epccs/RPUpi/Hardware/Design/MultiDrop.sch

## EAGLE design Hardware/Design/MultiDrop.sch (2018-09-16)

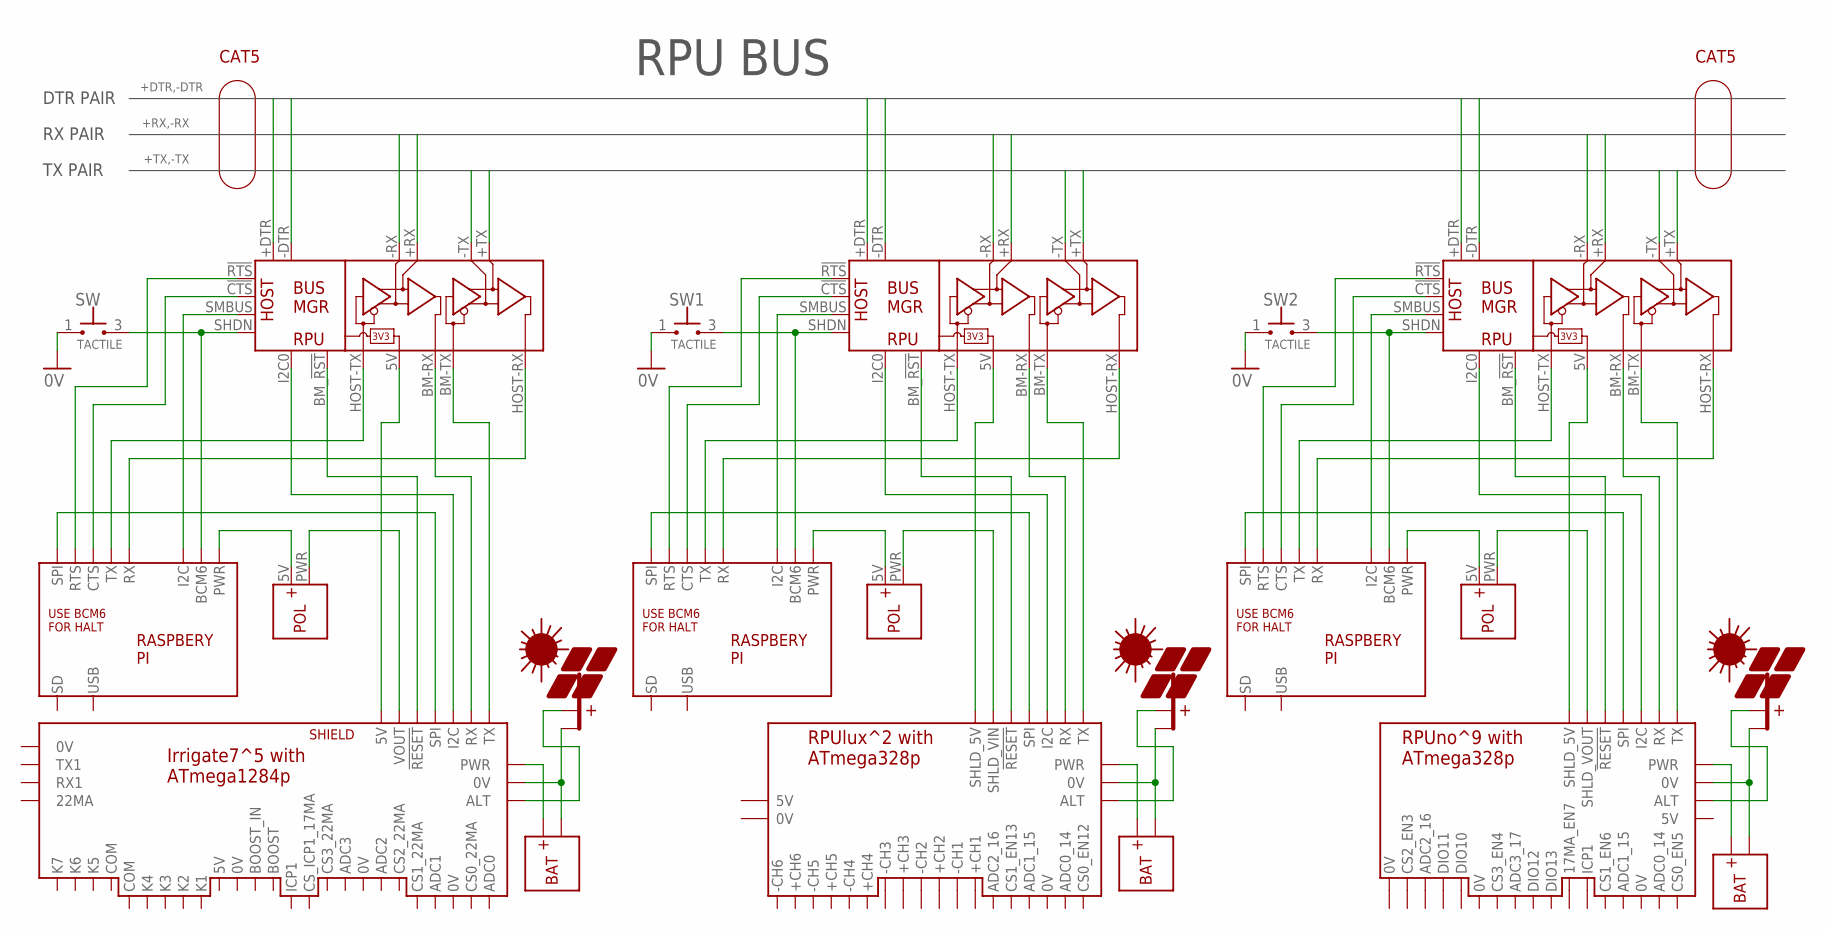
[picture p39: schematic MultiDrop.sch]

Parts:
BM1: RPUNO; NA-30
PV1, PV2, PV4: PV; NA-30
SW, SW1, SW2: TACTILE; KS11
U$1: IRRIGATE7; WITH_RPU_NAMES
U$2: RPULUX; WITH_RPU_NAMES
U$3, U$6, U$8: BUS_MGR; WITH_RPU_NAMES
U$4, U$7, U$9: BAT; NA-30
U$5, U$10, U$11: PI; NA-30
U$12, U$13, U$14: POL; WITH_RPU_NAMES

Connections:
0V: SW.1, SW1.1, SW2.1
+DTR: U$8.+DTR
+DTR1: U$3.+DTR
+DTR2: U$6.+DTR
+RX: U$8.+RX
+RX1: U$3.+RX
+RX2: U$6.+RX
+TX: U$8.+TX
+TX1: U$3.+TX
+TX2: U$6.+TX
-DTR: U$8.-DTR
-DTR1: U$3.-DTR
-DTR2: U$6.-DTR
-RX: U$8.-RX
-RX1: U$3.-RX
-RX2: U$6.-RX
-TX: U$8.-TX
-TX1: U$3.-TX
-TX2: U$6.-TX
unnamed: U$1.TX, U$8.BM-TX (BM_TX)
unnamed: U$1.RX, U$8.BM-RX (BM_RX)
unnamed: U$1.SHLD_VOUT (VOUT), U$12.PWR (VIN)
unnamed: U$8.SMBUS, U$11.8 (I2C)
unnamed: SW.3, U$8.SHDN, U$11.7 (BCM6)
unnamed: U$1.SPI, U$11.10 (SPI)
unnamed: PV1.2 (-PV), U$1.0V@PWR (0V), U$4.2 (-BAT)
unnamed: U$8.HOST-RX (HOST_RX), U$11.3 (RX)
unnamed: U$8.HOST-TX (HOST_TX), U$11.4 (TX)
unnamed: U$2.TX, U$3.BM-TX (BM_TX)
unnamed: U$2.RX, U$3.BM-RX (BM_RX)
unnamed: U$1.PWR, U$4.1 (+BAT)
unnamed: U$8.!CTS, U$11.1 (CTS)
unnamed: U$3.HOST-RX (HOST_RX), U$5.3 (RX)
unnamed: PV1.1 (+PV), U$1.AUX (ALT)
unnamed: U$8.!RTS, U$11.2 (RTS)
unnamed: U$3.HOST-TX (HOST_TX), U$5.4 (TX)
unnamed: U$2.SHLD_5V, U$3.5V (PWR)
unnamed: U$2.!RESET, U$3.BM_!RST! (BM-!RST!)
unnamed: U$2.I2C, U$3.I2C0
unnamed: U$2.SHLD_VOUT (SHLD_VIN), U$13.PWR (VIN)
unnamed: U$2.SPI, U$5.10 (SPI)
unnamed: U$3.SMBUS, U$5.8 (I2C)
unnamed: SW1.3, U$3.SHDN, U$5.7 (BCM6)
unnamed: U$3.!CTS, U$5.1 (CTS)
unnamed: U$3.!RTS, U$5.2 (RTS)
unnamed: BM1.1 (TX), U$6.BM-TX (BM_TX)
unnamed: BM1.2 (RX), U$6.BM-RX (BM_RX)
unnamed: U$1.SHLD_5V (5V), U$8.5V (PWR)
unnamed: U$1.!RESET, U$8.BM_!RST! (BM-!RST!)
unnamed: U$6.HOST-RX (HOST_RX), U$10.3 (RX)
unnamed: U$6.HOST-TX (HOST_TX), U$10.4 (TX)
unnamed: U$1.I2C, U$8.I2C0
unnamed: BM1.6 (SHLD_5V), U$6.5V (PWR)
unnamed: BM1.5 (!RESET), U$6.BM_!RST! (BM-!RST!)
unnamed: BM1.3 (I2C), U$6.I2C0
unnamed: BM1.7 (SHLD_VOUT), U$14.PWR (VIN)
unnamed: BM1.4 (SPI), U$10.10 (SPI)
unnamed: U$6.SMBUS, U$10.8 (I2C)
unnamed: SW2.3, U$6.SHDN, U$10.7 (BCM6)
unnamed: U$6.!CTS, U$10.1 (CTS)
unnamed: U$6.!RTS, U$10.2 (RTS)
unnamed: PV2.2 (-PV), U$2.0V@PWR (0V), U$9.2 (-BAT)
unnamed: U$2.PWR, U$9.1 (+BAT)
unnamed: PV2.1 (+PV), U$2.AUX (ALT)
unnamed: BM1.9 (0V), PV4.2 (-PV), U$7.2 (-BAT)
unnamed: BM1.8 (PWR), U$7.1 (+BAT)
unnamed: BM1.20 (ALT), PV4.1 (+PV)
unnamed: U$10.12 (PWR), U$14.5V
unnamed: U$5.12 (PWR), U$13.5V
unnamed: U$11.12 (PWR), U$12.5V

Notes on the sheet:
CAT5
DTR PAIR
RX PAIR
TX PAIR
RPU BUS
