epccs/RPUpi/Hardware/Design/Pi2AVR.sch

## EAGLE design Hardware/Design/Pi2AVR.sch (2018-09-16)

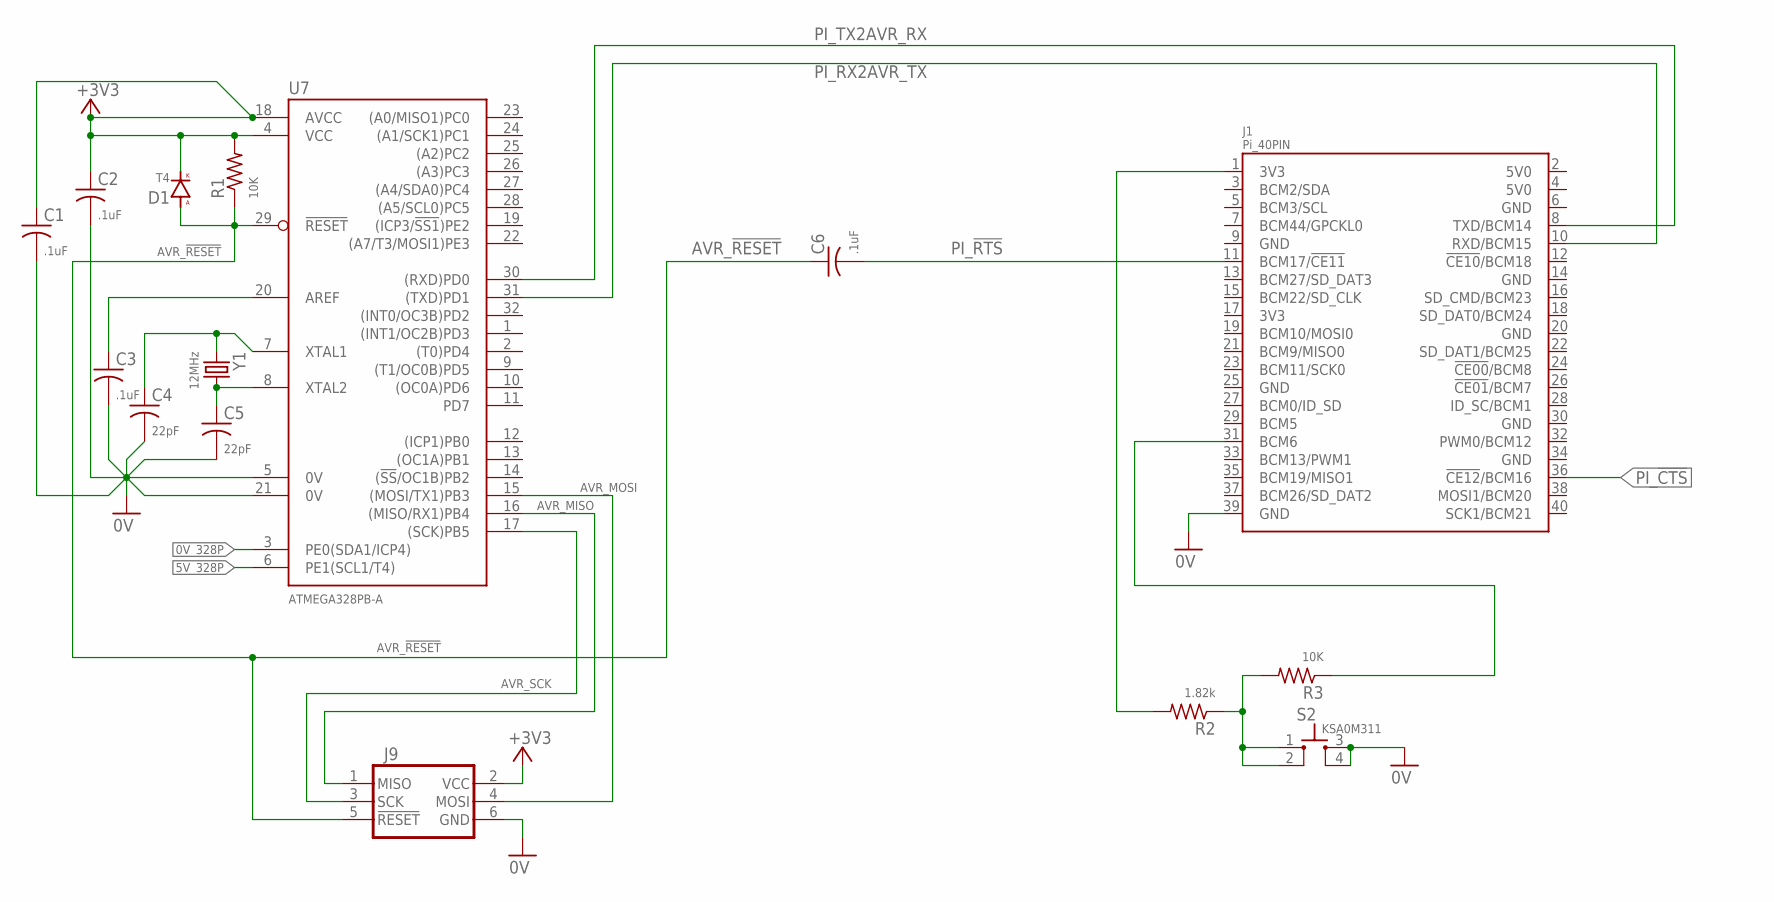
[picture p40: schematic Pi2AVR.sch]

Parts:
C1, C2, C3, C6: .1uF; C0603(1608)
C4, C5: 22pF; C0603(1608)
D1: T4; SOD123
J1: Pi_40PIN; RASPI_ZERO_V40PIN
J9: ISP-SPIPTH; ISP
R1, R3: 10K; C0805(2012)
R2: 1.82k; C0805(2012)
S2: KSA0M311; 0M311
U7: ATMEGA328PB-A; TQFP32-08
Y1: 12MHz; CSM-3X

Connections:
0V: C1.2, C2.2, C3.2, C4.2, C5.2, J1.39 (GND), J9.6 (GND), S2.3, S2.4, U7.5 (0V), U7.21 (0V)
0V_328P: U7.3 (PE0(SDA1/ICP4))
3V3@1: J1.1 (3V3), R2.2
5V_328P: U7.6 (PE1(SCL1/T4))
+3V3: C1.1, C2.1, D1.C (K), J9.2 (VCC), R1.2, U7.4 (VCC), U7.18 (AVCC)
AVR_!RESET: C6.1, D1.A, J9.5 (!RESET), R1.1, U7.29 (!RESET)
AVR_MISO: J9.1 (MISO), U7.16 ((MISO/RX1)PB4)
AVR_MOSI: J9.4 (MOSI), U7.15 ((MOSI/TX1)PB3)
AVR_SCK: J9.3 (SCK), U7.17 ((SCK)PB5)
MGR_AREF: C3.1, U7.20 (AREF)
unnamed: J1.31 (BCM6), R3.1
unnamed: R2.1, R3.2, S2.1, S2.2
PI_!CTS!: J1.36 (!CE12!/BCM16)
PI_!RTS!: C6.2, J1.11 (BCM17/!CE11!)
PI_RX2AVR_TX: J1.10 (RXD/BCM15), U7.31 ((TXD)PD1)
PI_TX2AVR_RX: J1.8 (TXD/BCM14), U7.30 ((RXD)PD0)
XTAL1: C4.1, U7.7 (XTAL1), Y1.1
XTAL2: C5.1, U7.8 (XTAL2), Y1.2
