epccs/RPUpi/Hardware/Design/Pi2AVR_wIOFF.sch

## EAGLE design Hardware/Design/Pi2AVR_wIOFF.sch (2018-09-16)

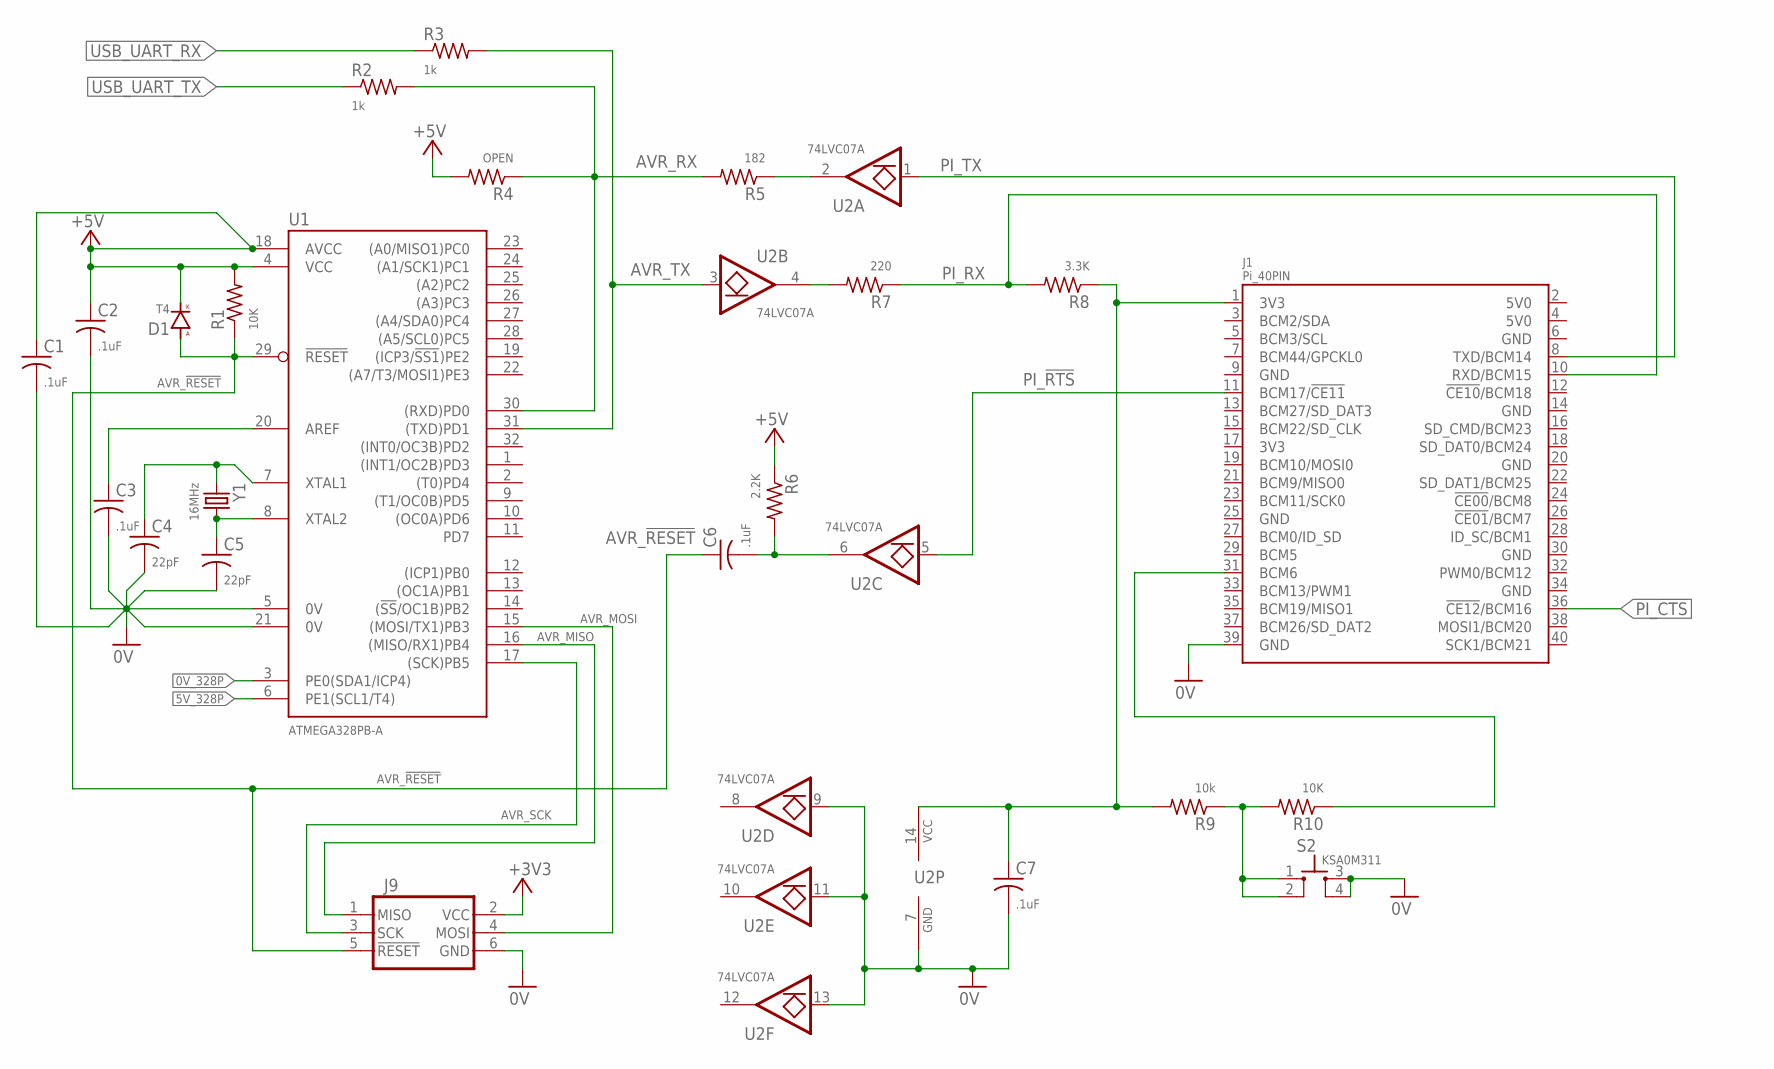
[picture p41: schematic Pi2AVR_wIOFF.sch]

Parts:
C1, C2, C3, C6, C7: .1uF; C0603(1608)
C4, C5: 22pF; C0603(1608)
D1: T4; SOD123
J1: Pi_40PIN; RASPI_ZERO_V40PIN
J9: ISP-SPIPTH; ISP
R1, R10: 10K; C0805(2012)
R2, R3: 1k; C0805(2012)
R4: OPEN; C0805(2012)
R5: 182; C0805(2012)
R6: 2.2K; C0805(2012)
R7: 220; C0805(2012)
R8: 3.3K; C0805(2012)
R9: 10k; C0805(2012)
S2: KSA0M311; 0M311
U1: ATMEGA328PB-A; TQFP32-08
U2: 74LVC07A; 14SOIC
Y1: 16MHz; CSM-3X

Connections:
0V: C1.2, C2.2, C3.2, C4.2, C5.2, C7.2, J1.39 (GND), J9.6 (GND), S2.3, S2.4, U1.5 (0V), U1.21 (0V), U2.7 (GND), U2.9 (I), U2.11 (I), U2.13 (I)
0V_328P: U1.3 (PE0(SDA1/ICP4))
3V3@1: C7.1, J1.1 (3V3), R8.1, R9.2, U2.14 (VCC)
5V_328P: U1.6 (PE1(SCL1/T4))
+3V3: J9.2 (VCC)
+5V: C1.1, C2.1, D1.C (K), R1.2, R4.2, R6.1, U1.4 (VCC), U1.18 (AVCC)
AVR_!RESET: C6.1, D1.A, J9.5 (!RESET), R1.1, U1.29 (!RESET)
AVR_MISO: J9.1 (MISO), U1.16 ((MISO/RX1)PB4)
AVR_MOSI: J9.4 (MOSI), U1.15 ((MOSI/TX1)PB3)
AVR_RX: R2.2, R4.1, R5.2, U1.30 ((RXD)PD0)
AVR_SCK: J9.3 (SCK), U1.17 ((SCK)PB5)
AVR_TX: R3.2, U1.31 ((TXD)PD1), U2.3 (I)
MGR_AREF: C3.1, U1.20 (AREF)
unnamed: J1.31 (BCM6), R10.1
unnamed: C6.2, R6.2, U2.6 (O)
unnamed: R5.1, U2.2 (O)
unnamed: R7.2, U2.4 (O)
unnamed: R9.1, R10.2, S2.1, S2.2
PI_!CTS!: J1.36 (!CE12!/BCM16)
PI_!RTS!: J1.11 (BCM17/!CE11!), U2.5 (I)
PI_RX: J1.10 (RXD/BCM15), R7.1, R8.2
PI_TX: J1.8 (TXD/BCM14), U2.1 (I)
USB_UART_RX: R3.1
USB_UART_TX: R2.1
XTAL1: C4.1, U1.7 (XTAL1), Y1.1
XTAL2: C5.1, U1.8 (XTAL2), Y1.2
